kauzerei/rig-htsized/stl_export/handle_rosette_mount.stl

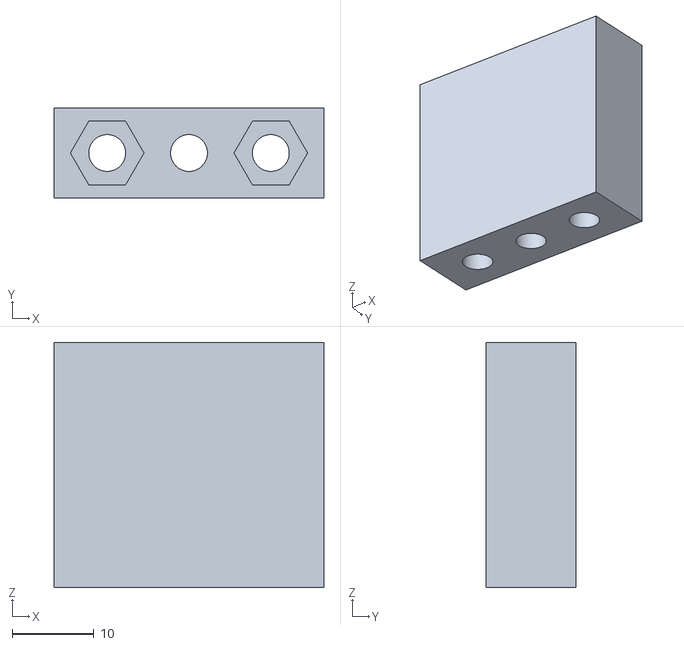
[picture p15: CAD file, 2024-06-10]
stl_export/handle_rosette_mount.stl
33.0 x 11.0 x 30.0
