kauzerei/rig-htsized/stl_export/spacer36.stl

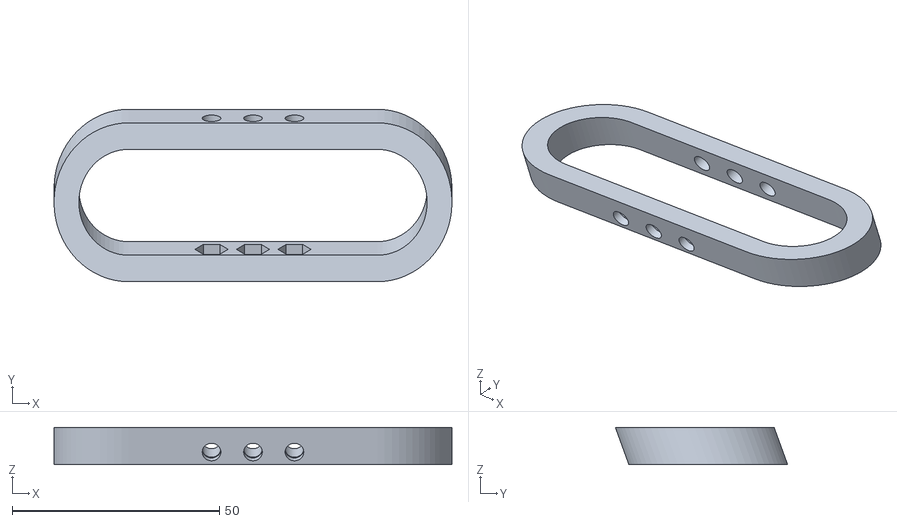
[picture p16: CAD file, 2024-06-05]
stl_export/spacer36.stl
96.0 x 41.6 x 9.00
