kauzerei/rig-htsized/stl_export/cokin_mount.stl

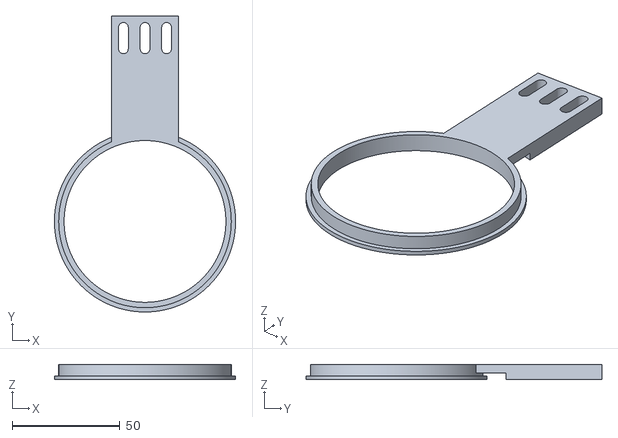
[picture p17: CAD file, 2024-05-31]
stl_export/cokin_mount.stl
84.0 x 137.2 x 7.00
