kauzerei/rig-htsized/stl_export/matte_box_mount.stl

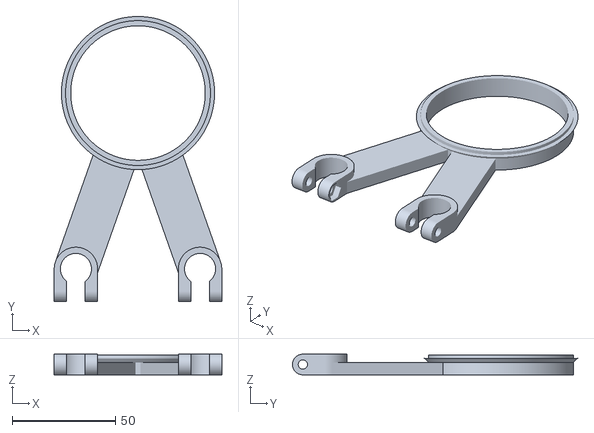
[picture p18: CAD file, 2024-05-31]
stl_export/matte_box_mount.stl
81.0 x 137.7 x 10.0
