kauzerei/rig-htsized/stl_export/spacer_block.stl

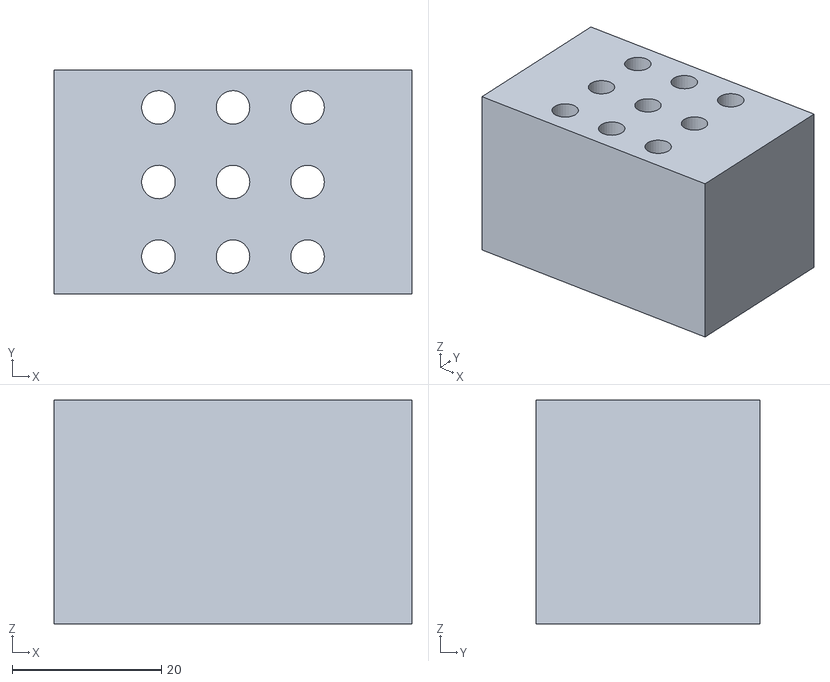
[picture p19: CAD file, 2024-05-31]
stl_export/spacer_block.stl
48.0 x 30.0 x 30.0
