kauzerei/rig-htsized/stl_export/matte_box_clamp.stl

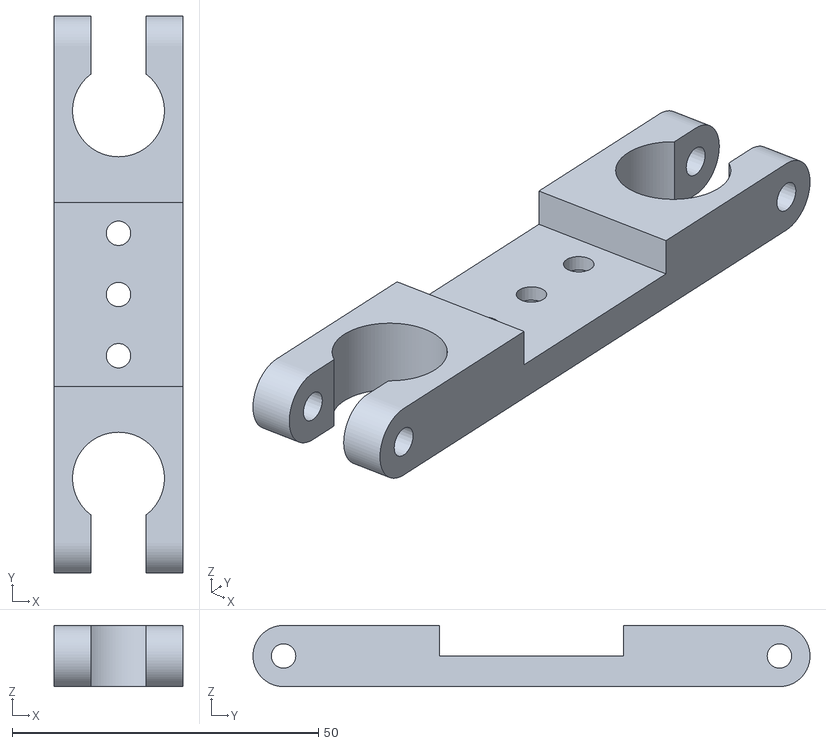
[picture p20: CAD file, 2024-05-31]
stl_export/matte_box_clamp.stl
21.0 x 91.0 x 10.0
