kauzerei/rig-htsized/stl_export/tube_coupler.stl

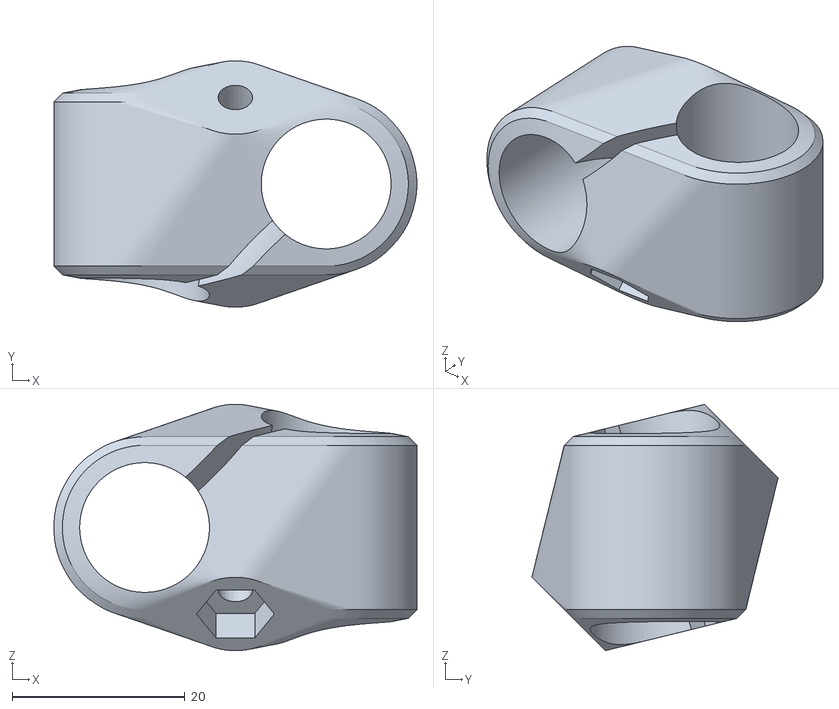
[picture p21: CAD file, 2024-05-18]
stl_export/tube_coupler.stl
42.0 x 28.5 x 28.5
