kauzerei/rig-htsized/stl_export/501_plate.stl

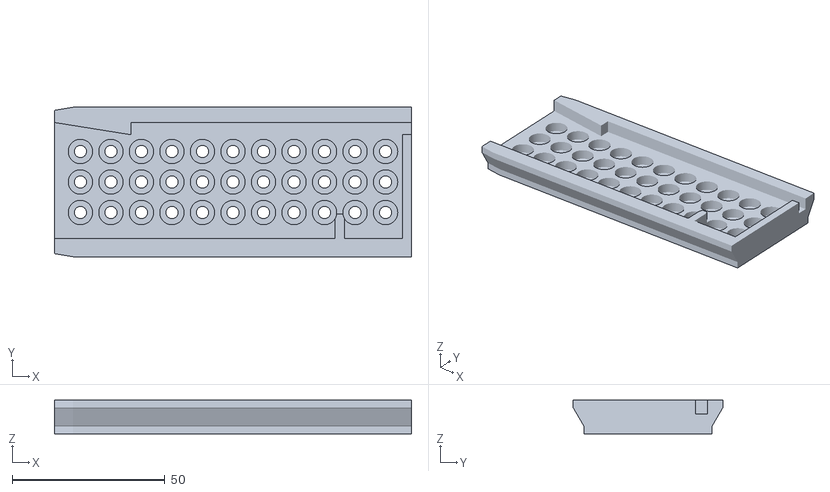
[picture p22: CAD file, 2024-05-18]
stl_export/501_plate.stl
117.0 x 49.0 x 11.0
