kauzerei/rig-htsized/stl_export/cage_olympus_e-pm1.stl

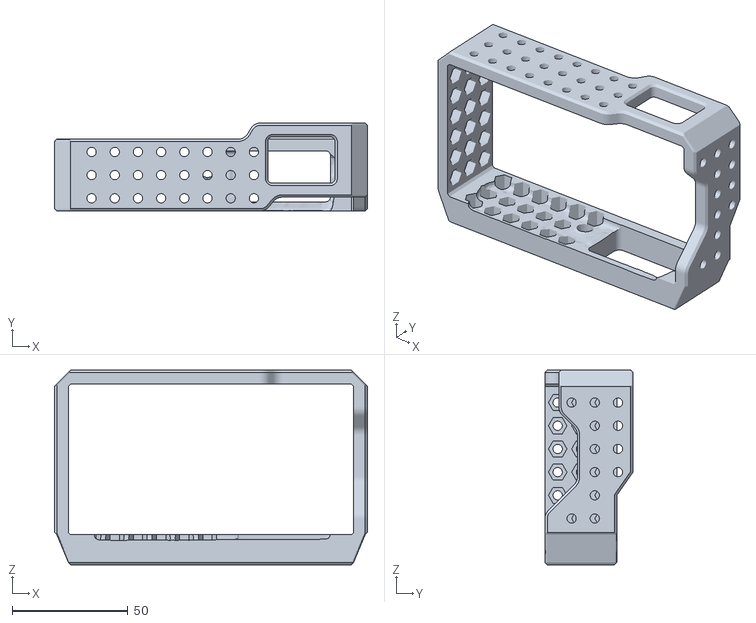
[picture p23: CAD file, 2024-05-18]
stl_export/cage_olympus_e-pm1.stl
135.0 x 38.0 x 84.0
