kauzerei/rig-htsized/stl_export/tube_clamp.stl

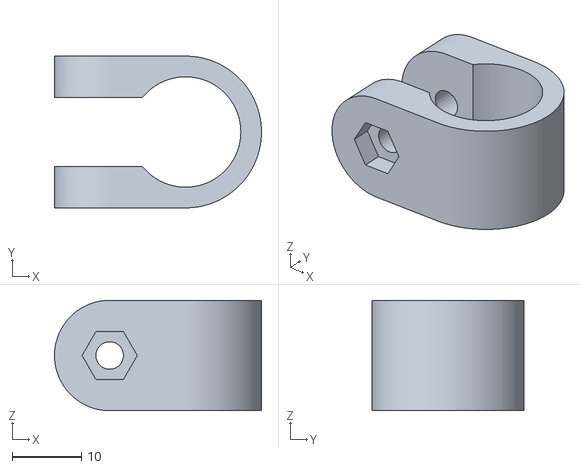
[picture p24: CAD file, 2024-05-18]
stl_export/tube_clamp.stl
30.0 x 22.0 x 16.0
