kauzerei/rig-htsized/stl_export/arm.stl

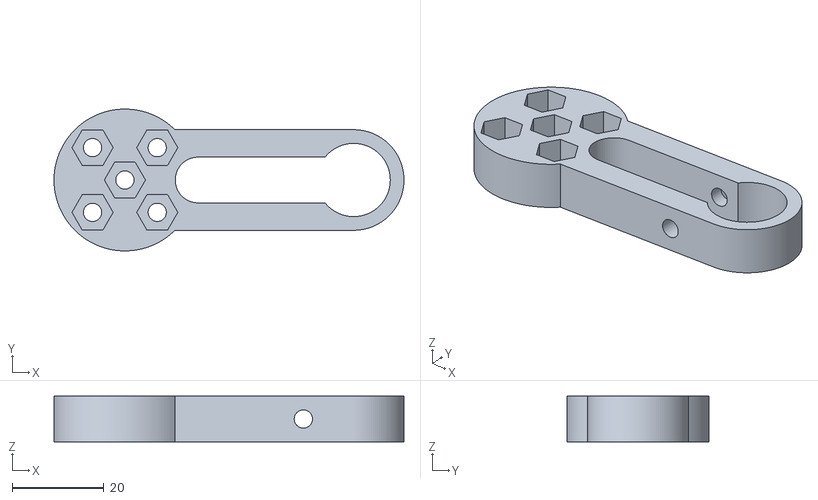
[picture p25: CAD file, 2024-05-18]
stl_export/arm.stl
76.5 x 31.0 x 10.0
