kauzerei/rig-htsized/stl_export/universal_clamp.stl

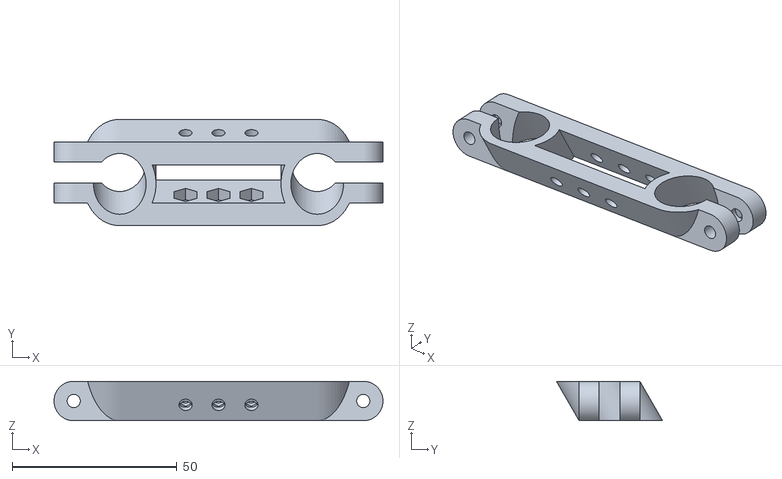
[picture p26: CAD file, 2024-04-24]
stl_export/universal_clamp.stl
100.0 x 32.3 x 12.0
