kauzerei/rig-htsized/stl_export/cage_sony_nex-f3.stl

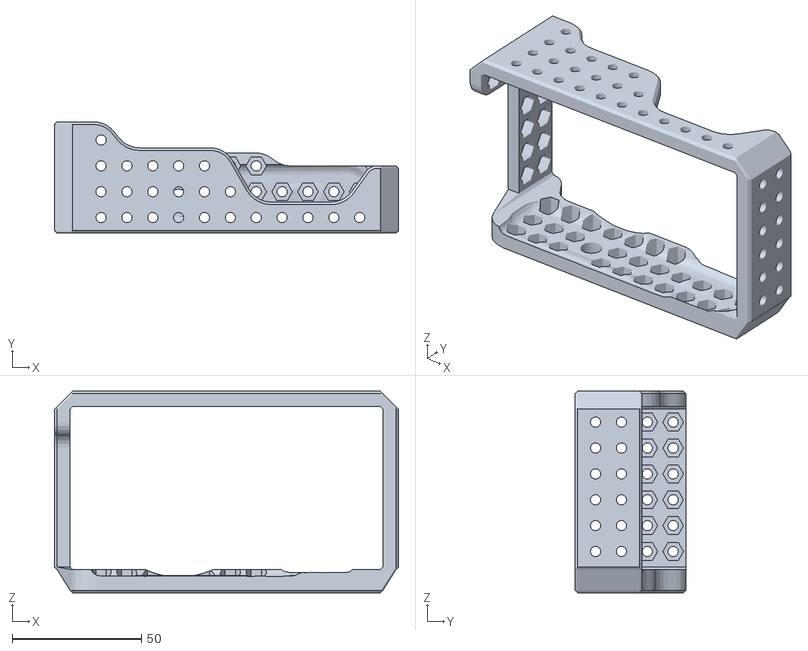
[picture p27: CAD file, 2024-04-23]
stl_export/cage_sony_nex-f3.stl
133.0 x 43.0 x 78.0
