kauzerei/rig-htsized/scad/rosette.scad

// Arri-Rosette-type Hirth joint. It does mesh perfectly with itself unlike some
// other designs on Thingiverse. To the best of my knowledge it follows exactly
// the shape of the real deal, but I'm too poor to actually purcase an Arri
// product to check. I use it to mount to narrow parts with cylindrical-headed
// screws. I'll make a standard rosette with countersunk holes some day
// thickness of the mounting plane underneath the joint
thickness = 0.5;
// vertical distance between mounting plate and lowest point of teeth, place for
// head of a screw
screw_head_space = 3.0;
// diameter of lowered part
screw_side_space_diameter = 16;
// diameter of mounting circle
bcd = 20;
// number of screws in circle
n_screws = 4;
// diameter of central hole
d_center = 4.0;
// diameter of mounting holes
d_circle = 4.0;
// diameter of screw head
d_head = 9.0;
// conical/cylindrical screw head switch
cylindrical = false;
// STANDARD IS 60, other numbers are not Arri-conpatible. Number of detents
hirth_n = 60;
// STANDARD IS 32, diameter
hirth_d = 32;
$fa = 1 / 1;
$fs = 1 / 2;
bissl = 1 / 100;
use <include/hirth.scad>
height = hirth_height(hirth_d / cos(180 / hirth_n), hirth_n, 90);
module screw_space(cylindrical = cylindrical) {
  if (cylindrical) {
    cylinder(d = d_circle, h = 100, center = true);
    cylinder(d = d_head, h = 100);
  } else {
    cylinder(d = d_circle, h = 100, center = true);
    cylinder(d1 = d_circle, d2 = d_head, h = (d_head - d_circle) / 2);
    translate([ 0, 0, (d_head - d_circle) / 2 - bissl ])
        cylinder(d = d_head, h = screw_head_space);
  }
}
module arri_rosette(thickness = 1.5, screw_head_space = 1,
                    screw_side_space_diameter = 16, bcd = 12, n_screws = 4,
                    d_center = 4, d_circle = 2.5, hirth_n = 30, hirth_d = 32) {
  difference() {
    union() {
      translate([ 0, 0, thickness + screw_head_space ]) intersection() {
        hirth(d = hirth_d + 1, n = hirth_n, w = 90);
        cylinder(d1 = hirth_d,
                 d2 = hirth_d - 2 * hirth_height(hirth_d / cos(180 / hirth_n),
                                                 hirth_n, 90),
                 h = hirth_height(hirth_d / cos(180 / hirth_n), hirth_n, 90),
                 $fn = hirth_n);
      }
      cylinder(h = thickness + screw_head_space, d = hirth_d, $fn = hirth_n);
    }
    translate([ 0, 0, thickness ])
        cylinder(d = screw_side_space_diameter,
                 h = screw_head_space +
                     hirth_height(hirth_d / cos(180 / hirth_n), hirth_n, 90));
    for (i = [0:360 / n_screws:360 - 360 / n_screws])
      rotate([ 0, 0, i ]) translate([ bcd / 2, 0, thickness ])
          screw_space(cylindrical = cylindrical);
    translate([ 0, 0, -0.01 ]) cylinder(h = thickness + 0.02, d = d_center);
  }
}
arri_rosette(thickness = thickness, screw_head_space = screw_head_space,
             screw_side_space_diameter = screw_side_space_diameter, bcd = bcd,
             n_screws = n_screws, d_center = d_center, d_circle = d_circle,
             hirth_n = hirth_n, hirth_d);
